lordexe22/Guante-de-control-inalambrico/imagenes/Bateria duracell.jpg

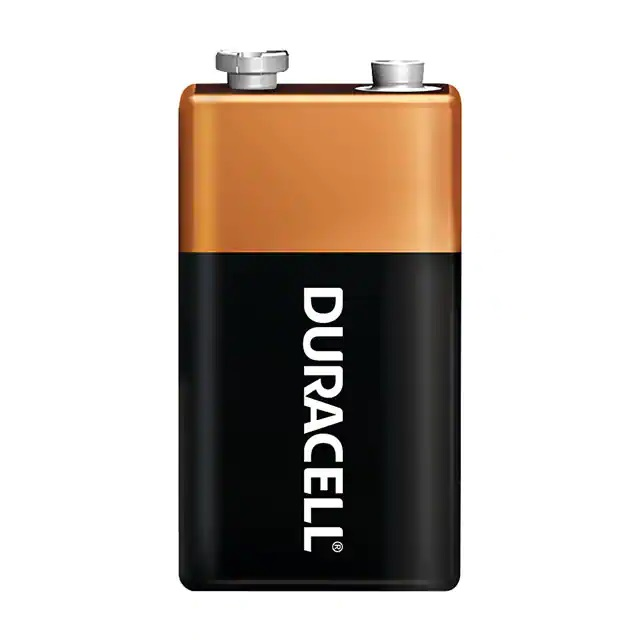
imagenes/Bateria duracell.jpg
