lordexe22/Guante-de-control-inalambrico/imagenes/Conexiones ESP32 Receptor.png

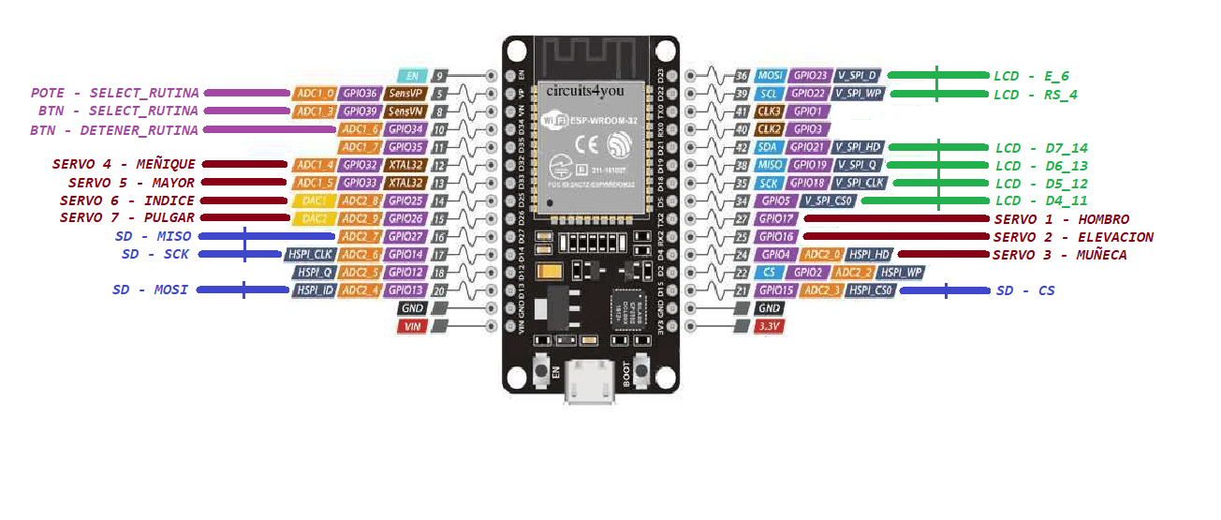
imagenes/Conexiones ESP32 Receptor.png
