lordexe22/Guante-de-control-inalambrico/imagenes/Conexiones ESP32.png

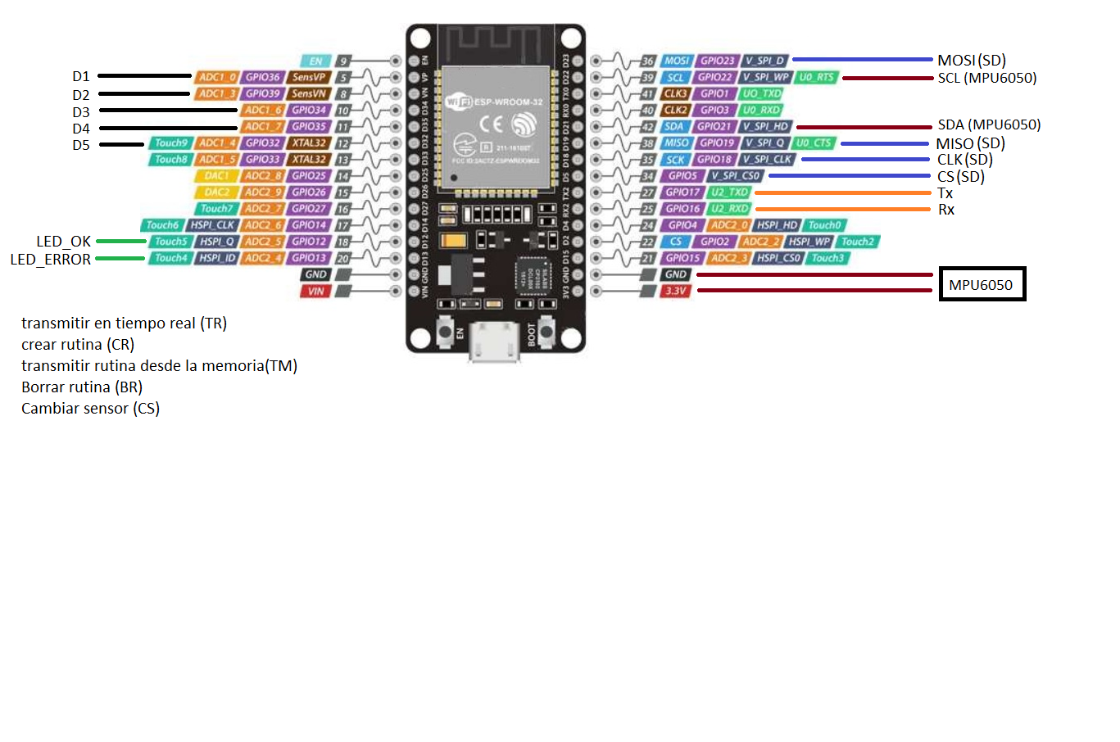
imagenes/Conexiones ESP32.png
