lordexe22/Guante-de-control-inalambrico/imagenes/ESP32-back.jpg

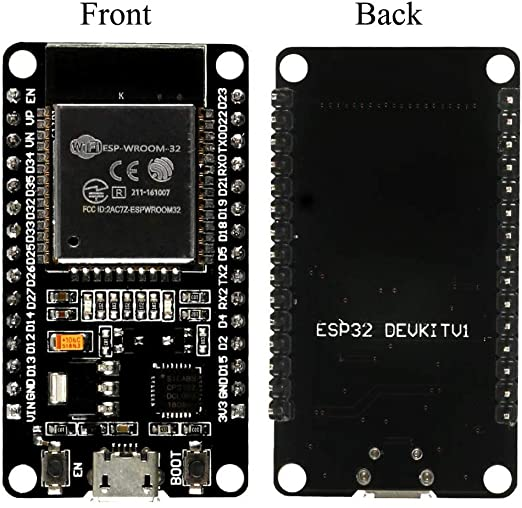
imagenes/ESP32-back.jpg
