lordexe22/Guante-de-control-inalambrico/imagenes/LCD 2x16 - Conexiones.png

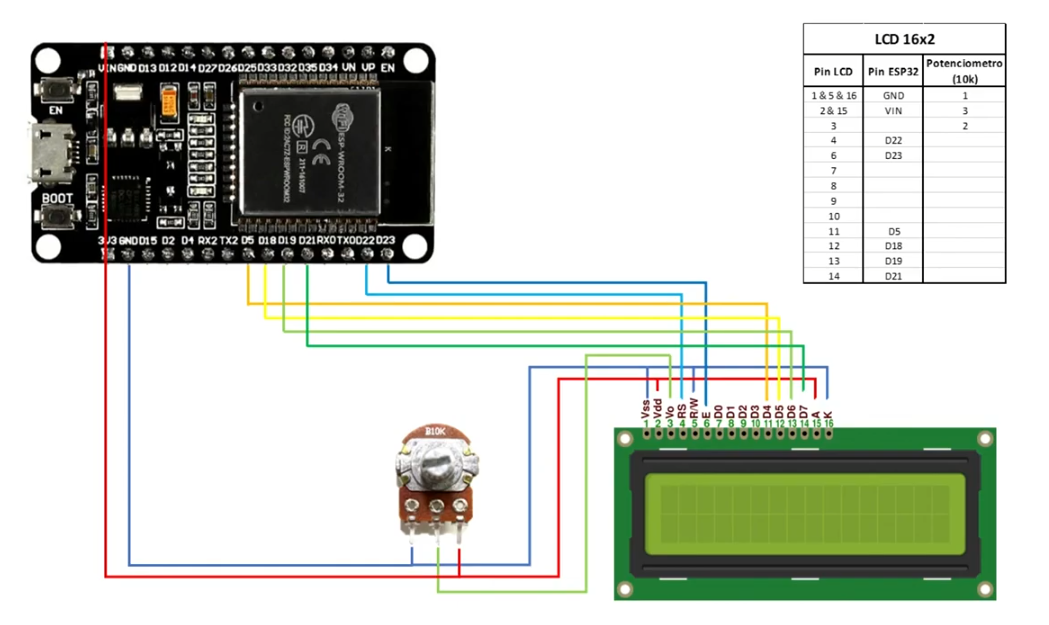
imagenes/LCD 2x16 - Conexiones.png
