lordexe22/Guante-de-control-inalambrico/imagenes/MPU6050-2.jpg

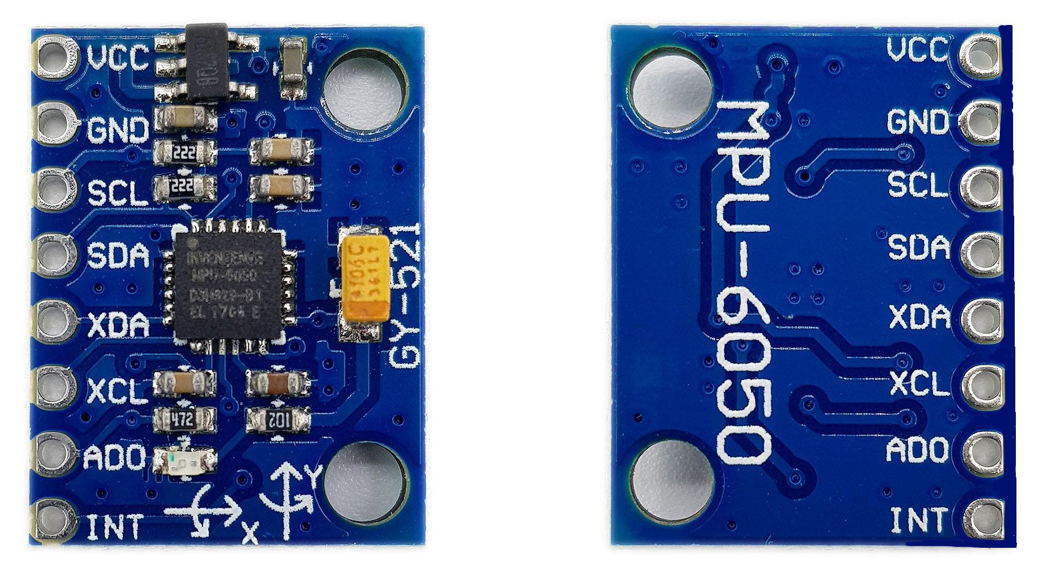
imagenes/MPU6050-2.jpg
