lordexe22/Guante-de-control-inalambrico/imagenes/MPU 6050.png

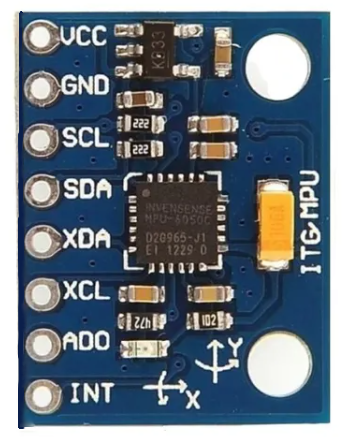
imagenes/MPU 6050.png
