lordexe22/Guante-de-control-inalambrico/imagenes/Sensor de giro - reverso.png

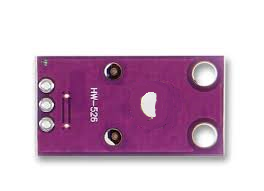
imagenes/Sensor de giro - reverso.png
