lordexe22/Guante-de-control-inalambrico/imagenes/Sensor de giro.png

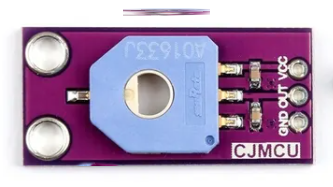
imagenes/Sensor de giro.png
