lordexe22/Guante-de-control-inalambrico/Informes/gif/error memoria.gif

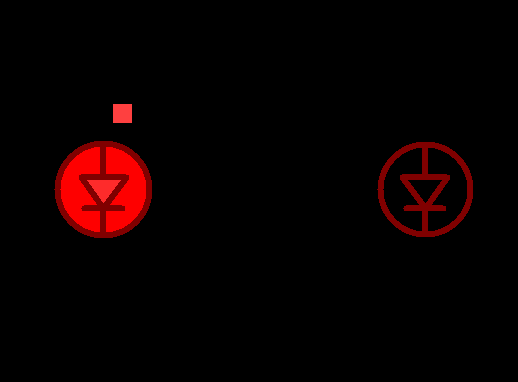
Informes/gif/error memoria.gif
