lordexe22/Guante-de-control-inalambrico/PCB/Modelos 3D/Leds/LED's 5mm TH 1.jpg

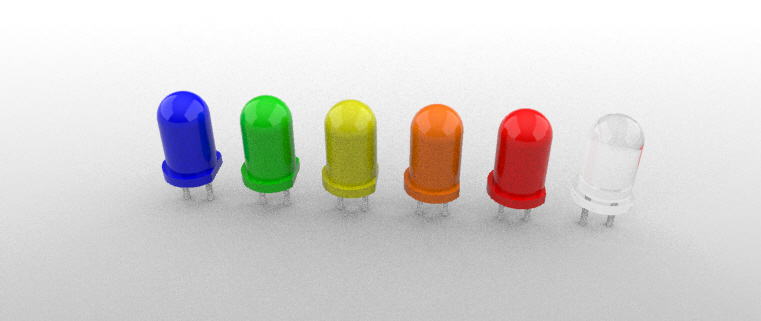
PCB/Modelos 3D/Leds/LED's 5mm TH 1.jpg
