lordexe22/Guante-de-control-inalambrico/sensores/ESP32-removebg-preview.png

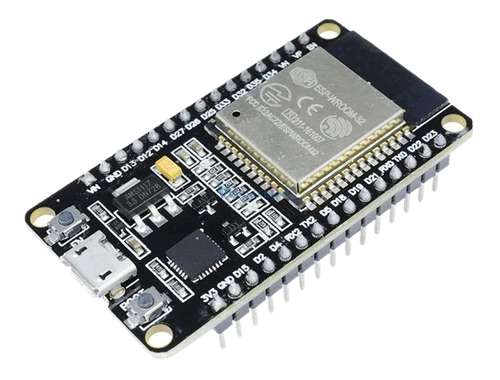
sensores/ESP32-removebg-preview.png
