lordexe22/Guante-de-control-inalambrico/sensores/ledes-removebg-preview.png

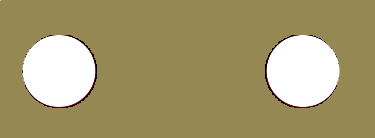
sensores/ledes-removebg-preview.png
