lordexe22/Guante-de-control-inalambrico/sensores/ledes.png

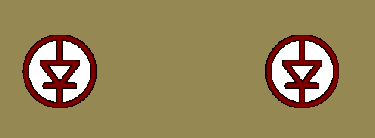
sensores/ledes.png
