lordexe22/Guante-de-control-inalambrico/sensores/linterna-removebg-preview.png

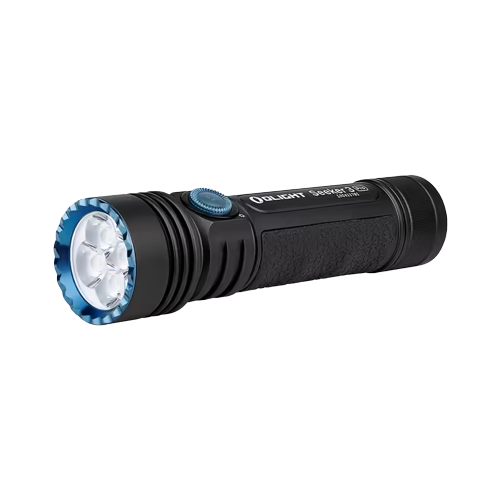
sensores/linterna-removebg-preview.png
