lordexe22/Guante-de-control-inalambrico/sensores/sensor de humedad.png

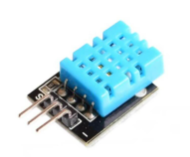
sensores/sensor de humedad.png
