lordexe22/Guante-de-control-inalambrico/sensores/sensor de humo.png

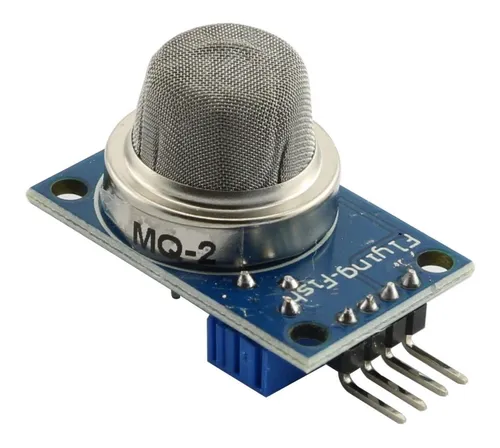
sensores/sensor de humo.png
