lordexe22/Guante-de-control-inalambrico/sensores/sensor de luz.png

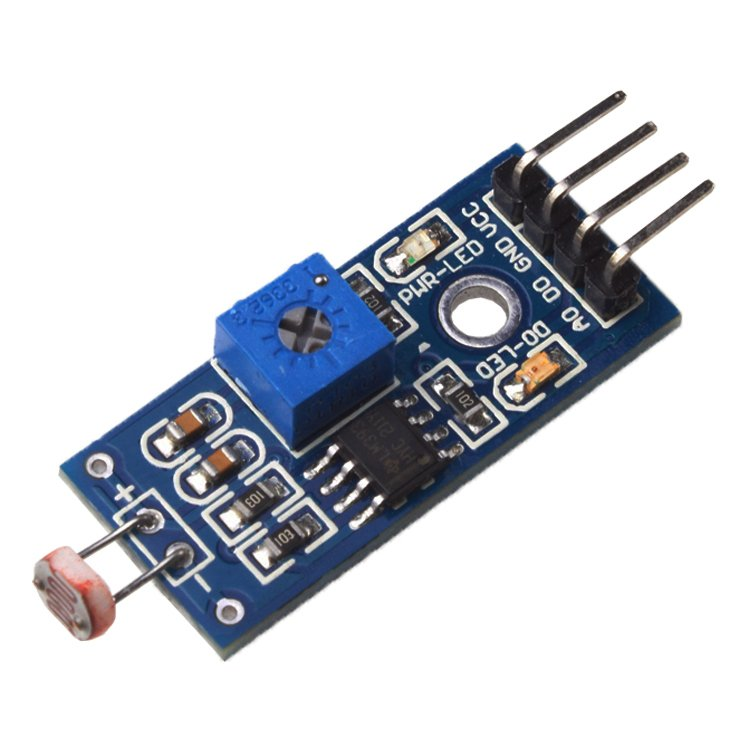
sensores/sensor de luz.png
