lordexe22/Guante-de-control-inalambrico/sensores/sensor de presion.png

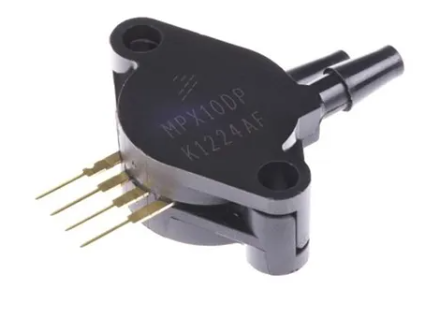
sensores/sensor de presion.png
