lordexe22/Guante-de-control-inalambrico/sensores/sensor de temperatura.png

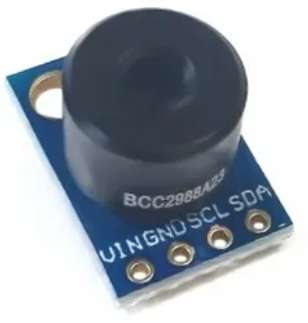
sensores/sensor de temperatura.png
