lordexe22/Guante-de-control-inalambrico/sensores/sensor ultrasonico.png

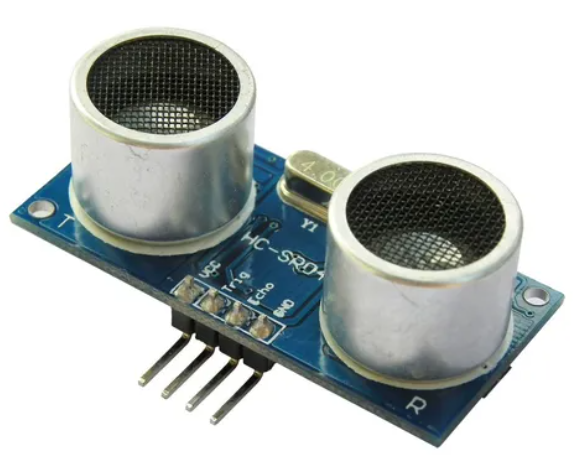
sensores/sensor ultrasonico.png
